Drundia666/ESP32-CYD-Bike-Computer/SD/settings.jpg

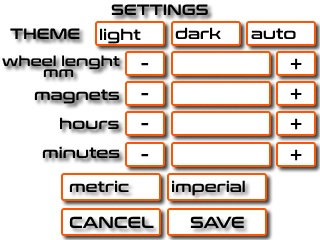
SD/settings.jpg
