Drundia666/ESP32-CYD-Bike-Computer/Assembly photos/correct_positioning_of_the_Hall_sensor.jpg

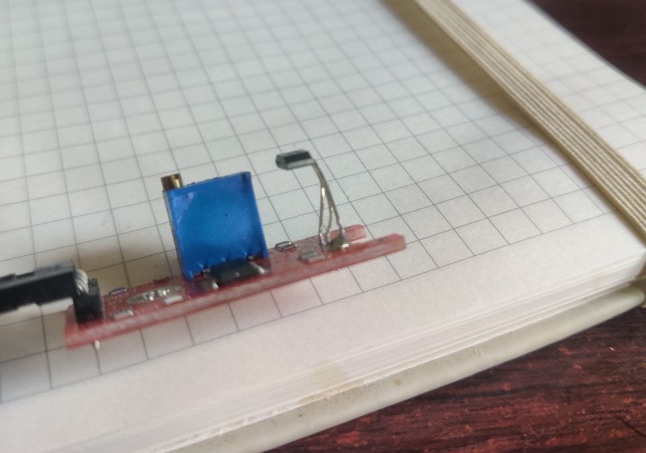
Assembly photos/correct_positioning_of_the_Hall_sensor.jpg
