Drundia666/ESP32-CYD-Bike-Computer/Assembly photos/photo_2026-09-20_20-18-35.jpg

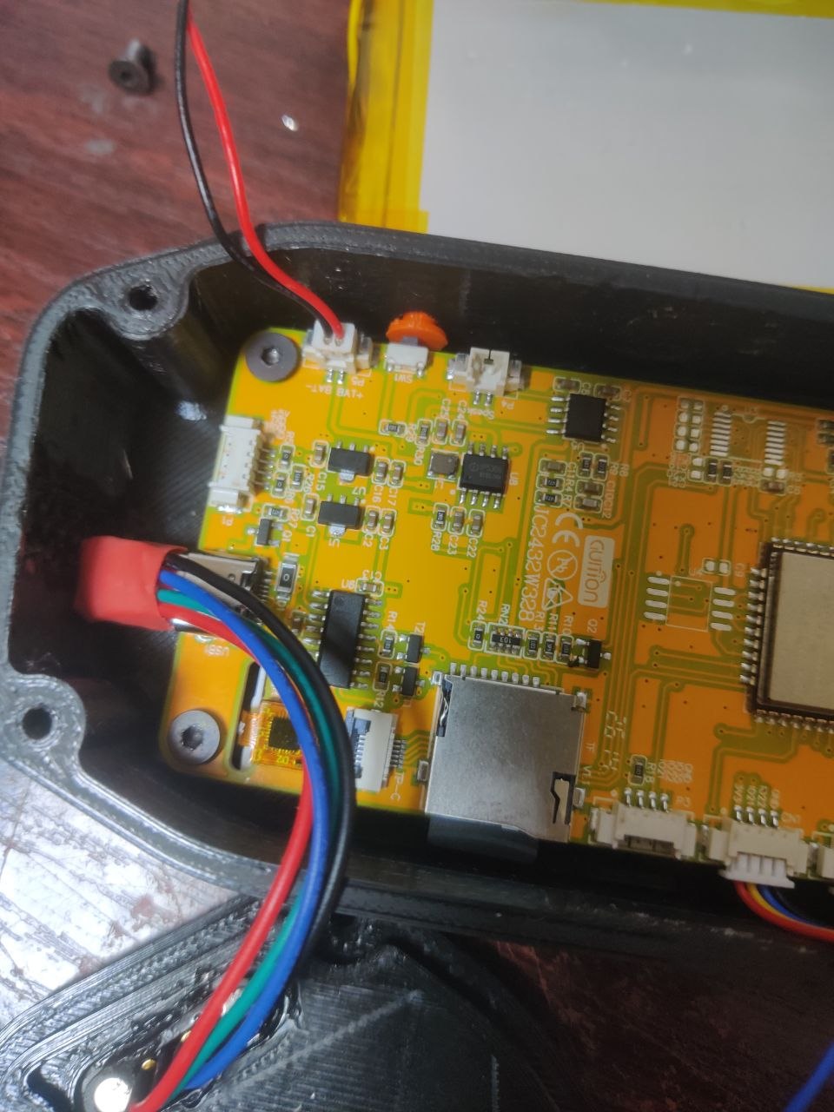
Assembly photos/photo_2026-09-20_20-18-35.jpg
