Drundia666/ESP32-CYD-Bike-Computer/Assembly photos/photo_2026-09-22_13-49-25.jpg

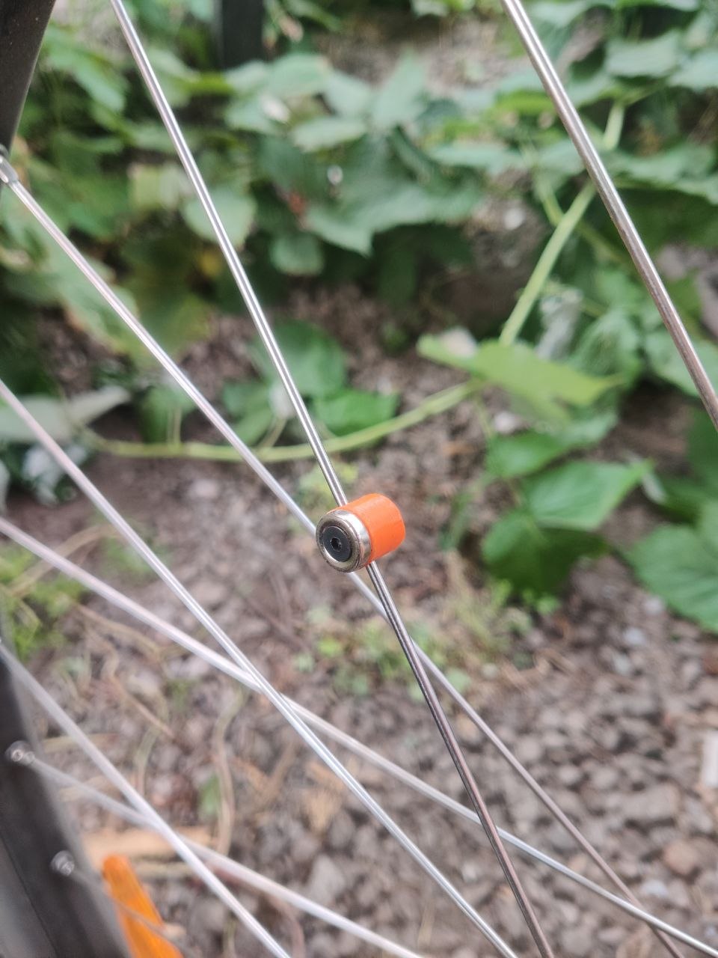
Assembly photos/photo_2026-09-22_13-49-25.jpg
